Kampi/Heartrate-DevKit-HW/production/heartrate-dk-CHECKED/Images/ZSWatch-Heartrate-DevKit-bottom.png

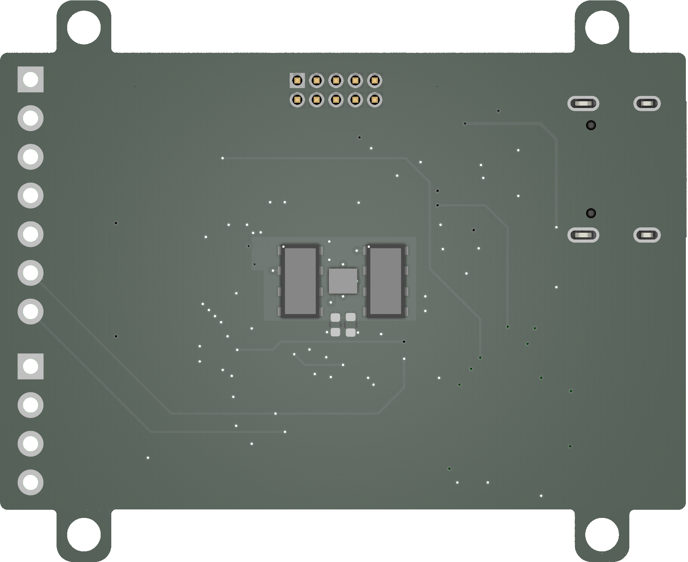
production/heartrate-dk-CHECKED/Images/ZSWatch-Heartrate-DevKit-bottom.png
