Kampi/Heartrate-DevKit-HW/production/heartrate-dk/HTML/images/cat_pdf_drill_map_ZSWatch-Heartrate-DevKit-NPTH_drill_map.png

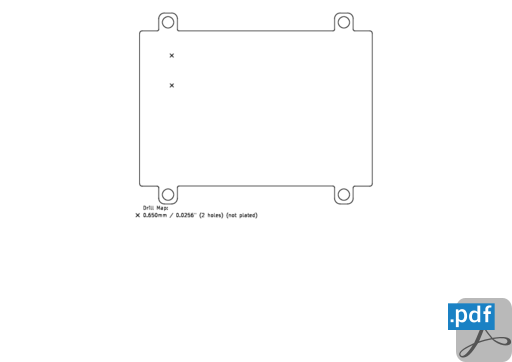
production/heartrate-dk/HTML/images/cat_pdf_drill_map_ZSWatch-Heartrate-DevKit-NPTH_drill_map.png
